herraa1/gbs-daughter-board-v2/images/IMG_5840.png

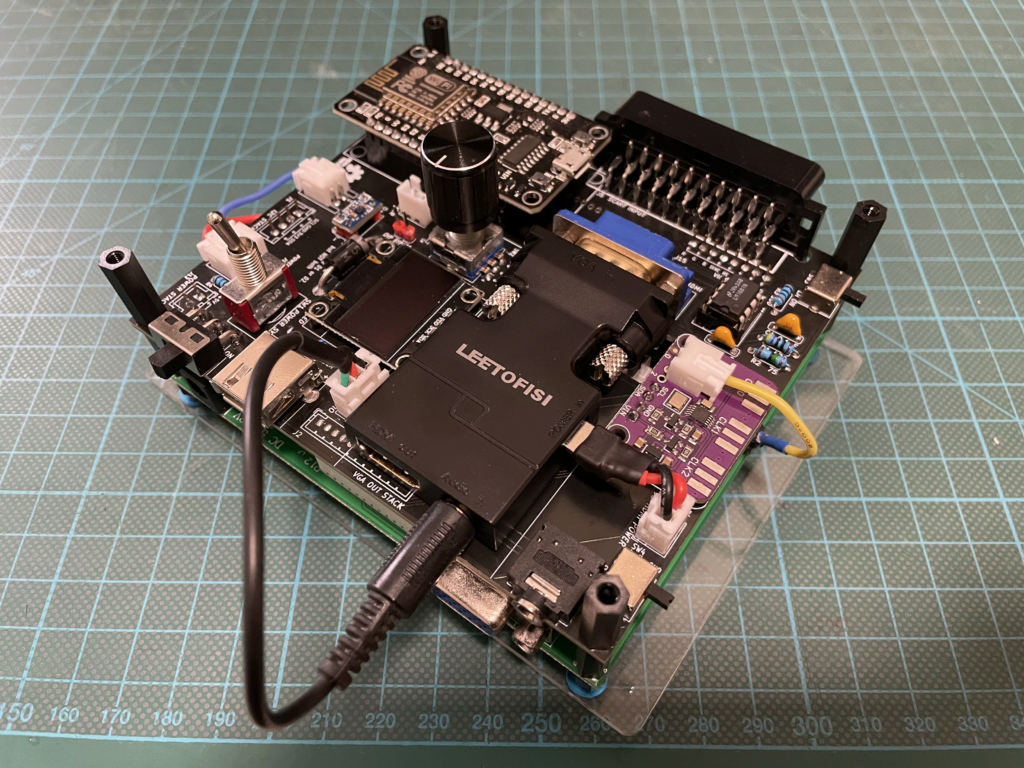
images/IMG_5840.png
