herraa1/gbs-daughter-board-v2/images/IMG_5847.png

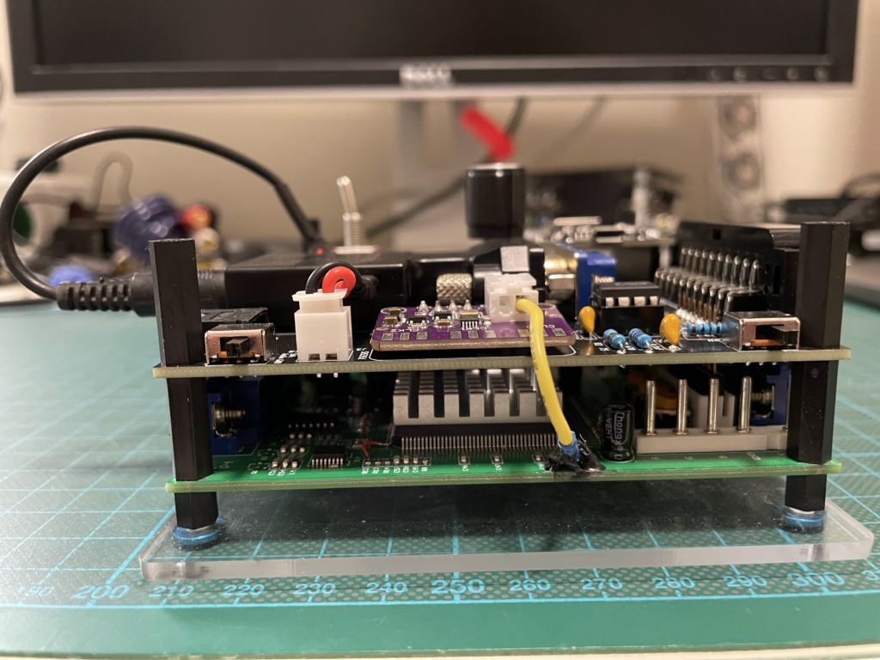
images/IMG_5847.png
